matt199394/c64esp32cart/c64esp32Cart/chars.c

#include <stdint.h>

const uint8_t chars[2048] = {
	0xFF, 0xFF, 0xFF, 0xFF, 0xFF, 0xFF, 0xFF, 0xFF,
	0xF8, 0xE0, 0xC0, 0xC3, 0x87, 0x87, 0x84, 0x84,
	0x80, 0x80, 0x80, 0x87, 0x87, 0x87, 0x84, 0x87,
	0xF8, 0xE0, 0xC0, 0xC3, 0x87, 0x87, 0x87, 0x87,
	0x80, 0x80, 0x80, 0xFF, 0x87, 0x87, 0x87, 0x87,
	0xC0, 0x80, 0x80, 0xFF, 0x87, 0x80, 0x80, 0x80,
	0xC0, 0x80, 0x80, 0xFF, 0x87, 0x80, 0x80, 0x80,
	0xC0, 0x80, 0x80, 0xFF, 0x87, 0x87, 0x87, 0x87,
	0x87, 0x87, 0x87, 0x87, 0x87, 0x87, 0x84, 0x84,
	0x80, 0x80, 0x80, 0xFF, 0xFC, 0xFC, 0xFC, 0xFC,
	0xFC, 0xFC, 0xFC, 0xFF, 0xFF, 0xFF, 0xFF, 0x87,
	0x87, 0x87, 0x87, 0x87, 0x86, 0x84, 0x84, 0x84,
	0x87, 0x87, 0x87, 0x87, 0x87, 0x87, 0x87, 0x87,
	0x87, 0x83, 0x81, 0x80, 0x80, 0x84, 0x86, 0x87,
	0x81, 0x81, 0x80, 0x80, 0x80, 0x84, 0x84, 0x86,
	0xF8, 0xE0, 0xC0, 0xC3, 0x87, 0x87, 0x87, 0x87,
	0x80, 0x80, 0x80, 0x87, 0x87, 0x87, 0x84, 0x84,
	0xF8, 0xE0, 0xC0, 0xC3, 0x87, 0xC3, 0xC0, 0xE0,
	0x80, 0x80, 0x80, 0x87, 0x87, 0x87, 0x84, 0x84,
	0xF8, 0xE0, 0xE0, 0xFF, 0xC3, 0xE0, 0xE0, 0xF8,
	0x80, 0x80, 0x80, 0xFC, 0xFC, 0xFC, 0xFC, 0xFC,
	0x87, 0x87, 0x87, 0x87, 0x87, 0x87, 0x87, 0x87,
	0x87, 0x87, 0x87, 0x87, 0x87, 0xC3, 0xC3, 0xE1,
	0x87, 0x87, 0x87, 0x87, 0x87, 0x87, 0x86, 0x84,
	0x87, 0x87, 0xC3, 0xE1, 0xF1, 0xFA, 0xFC, 0xF8,
	0x87, 0x87, 0x87, 0x87, 0x87, 0xC3, 0xC0, 0xE0,
	0x80, 0x80, 0x80, 0xFF, 0xFE, 0xFC, 0xF8, 0xF0,
	0xFF, 0xFF, 0xFF, 0xFF, 0xFF, 0xFF, 0xFF, 0xFF,
	0xFF, 0xFF, 0xFF, 0xFF, 0xFF, 0xFF, 0xFF, 0xFF,
	0xFF, 0xFF, 0xFF, 0xFF, 0xFF, 0xFF, 0xFF, 0xFF,
	0xFF, 0xFF, 0xFF, 0xFF, 0xFF, 0xFF, 0xFF, 0xFF,
	0xFF, 0xFF, 0xFF, 0xFF, 0xFF, 0xFF, 0xFF, 0xFF,
	0xFF, 0xFF, 0xFF, 0xFF, 0xFF, 0xFF, 0xFF, 0xFF,
	0xFC, 0xFC, 0xFC, 0xFC, 0xFC, 0xFC, 0xFC, 0xFC,
	0xFF, 0xFF, 0xFF, 0xFF, 0xFF, 0xFF, 0xFF, 0xFF,
	0xFF, 0xFF, 0xC3, 0xC3, 0xC3, 0x80, 0x80, 0xC3,
	0xFF, 0xFF, 0xFF, 0xFF, 0xFF, 0xFF, 0xFF, 0xFF,
	0xFF, 0xFF, 0x87, 0x87, 0x87, 0xFE, 0xFC, 0xF8,
	0xFF, 0xFF, 0xFF, 0xFF, 0xFF, 0xFF, 0xFF, 0xFF,
	0xFF, 0xFE, 0xFC, 0xF8, 0xF8, 0xF9, 0xFF, 0xFF,
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
};
