matt199394/c64esp32cart/c64esp32Cart/supermonA000.c

#include <stdint.h>

const uint8_t supermonA000[2820] = {
	0x00, 0xA0, 0xA0, 0x20, 0x20, 0x84, 0xA9, 0xAD,
	0x00, 0xAB, 0x85, 0xC1, 0xAD, 0x01, 0xAB, 0x85,
	0xC2, 0x20, 0x0E, 0xA8, 0xA9, 0x00, 0xA2, 0x06,
	0xA0, 0x03, 0x20, 0x48, 0xA8, 0x20, 0xDD, 0xA6,
	0xAD, 0xFE, 0xAA, 0x8D, 0x16, 0x03, 0xAD, 0xFF,
	0xAA, 0x8D, 0x17, 0x03, 0xA9, 0x80, 0x20, 0x90,
	0xFF, 0x00, 0xA2, 0x05, 0x68, 0x9D, 0x28, 0x02,
	0xCA, 0x10, 0xF9, 0xD8, 0xBA, 0x8E, 0x2E, 0x02,
	0x58, 0xA0, 0x00, 0x20, 0x71, 0xA9, 0xA9, 0x3B,
	0x20, 0xD2, 0xFF, 0xA9, 0x20, 0x20, 0xD2, 0xFF,
	0xAD, 0x28, 0x02, 0x20, 0xF6, 0xA6, 0xA0, 0x01,
	0xB9, 0x28, 0x02, 0x20, 0xD2, 0xA6, 0xC8, 0xC0,
	0x07, 0x90, 0xF5, 0x20, 0xDD, 0xA6, 0xA2, 0x00,
	0x8E, 0x31, 0x02, 0x20, 0xCF, 0xFF, 0x9D, 0x00,
	0x02, 0xE8, 0xE0, 0x27, 0xB0, 0x1C, 0xC9, 0x0D,
	0xD0, 0xF1, 0xA9, 0x00, 0x9D, 0xFF, 0x01, 0x20,
	0x1E, 0xA7, 0xF0, 0xDF, 0xC9, 0x20, 0xF0, 0xF7,
	0xA2, 0x16, 0xDD, 0xC2, 0xAA, 0xF0, 0x0B, 0xCA,
	0x10, 0xF8, 0xA0, 0x1E, 0x20, 0x84, 0xA9, 0x4C,
	0x61, 0xA0, 0xE0, 0x13, 0xB0, 0x12, 0xE0, 0x0F,
	0xB0, 0x14, 0x8A, 0x0A, 0xAA, 0xBD, 0xD9, 0xAA,
	0x48, 0xBD, 0xD8, 0xAA, 0x48, 0x4C, 0xFF, 0xA5,
	0x8D, 0x32, 0x02, 0x4C, 0x81, 0xA2, 0x4C, 0xC3,
	0xA7, 0x4C, 0xB7, 0x74, 0xB0, 0x08, 0x20, 0x38,
	0xA7, 0x20, 0xFF, 0xA5, 0x90, 0x06, 0xA9, 0x0B,
	0x85, 0xC1, 0xD0, 0x0E, 0x20, 0x41, 0xA7, 0x90,
	0x1E, 0xA2, 0x03, 0x46, 0xC2, 0x66, 0xC1, 0xCA,
	0xD0, 0xF9, 0x20, 0xE1, 0xFF, 0xF0, 0x0D, 0x20,
	0x5D, 0xA1, 0xA9, 0x08, 0x20, 0x77, 0xA7, 0x20,
	0x4F, 0xA7, 0xB0, 0xEE, 0x4C, 0x61, 0xA0, 0x4C,
	0x90, 0xA0, 0x20, 0x8F, 0xA7, 0xA0, 0x00, 0x20,
	0xFF, 0xA5, 0xB0, 0x0A, 0xA5, 0xC1, 0x99, 0x2A,
	0x02, 0xC8, 0xC0, 0x05, 0x90, 0xF1, 0x4C, 0x61,
	0xA0, 0xB0, 0x13, 0x20, 0x38, 0xA7, 0xA0, 0x00,
	0x20, 0xFF, 0xA5, 0xB0, 0x09, 0xA5, 0xC1, 0x91,
	0xC3, 0xC8, 0xC0, 0x08, 0x90, 0xF2, 0xA9, 0x91,
	0x20, 0xD2, 0xFF, 0x20, 0x5D, 0xA1, 0x4C, 0x61,
	0xA0, 0xAE, 0x2E, 0x02, 0x9A, 0x20, 0x8F, 0xA7,
	0x78, 0xAD, 0x28, 0x02, 0x48, 0xAD, 0x29, 0x02,
	0x48, 0xAD, 0x2A, 0x02, 0x48, 0xAD, 0x2B, 0x02,
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
};
